likeablob/endless-endless-eight/ulp/ulp_common.h

#define PM_VBAT_TH_WAKE 2158      // 3900 * 4095 / 3700 / 2
#define PM_VBAT_TH_SLEEP 2075     // 3750 * 4095 / 3700 / 2
#define PM_VBAT_TH_EMERGENCY 2019 // 3550 * 4095 / 3700 / 2

#define PM_STATUS_PERIODIC_TASK_REQ 0x1
#define PM_STATUS_EMERGENCY_TASK_REQ 0x2
#define PM_STATUS_WAKE_VOLTAGE_SATISFIED 0x4
